ska-sa/mezzanine_cards/SFPP/release/REV0/A/SFP_Led_Mod.pdf

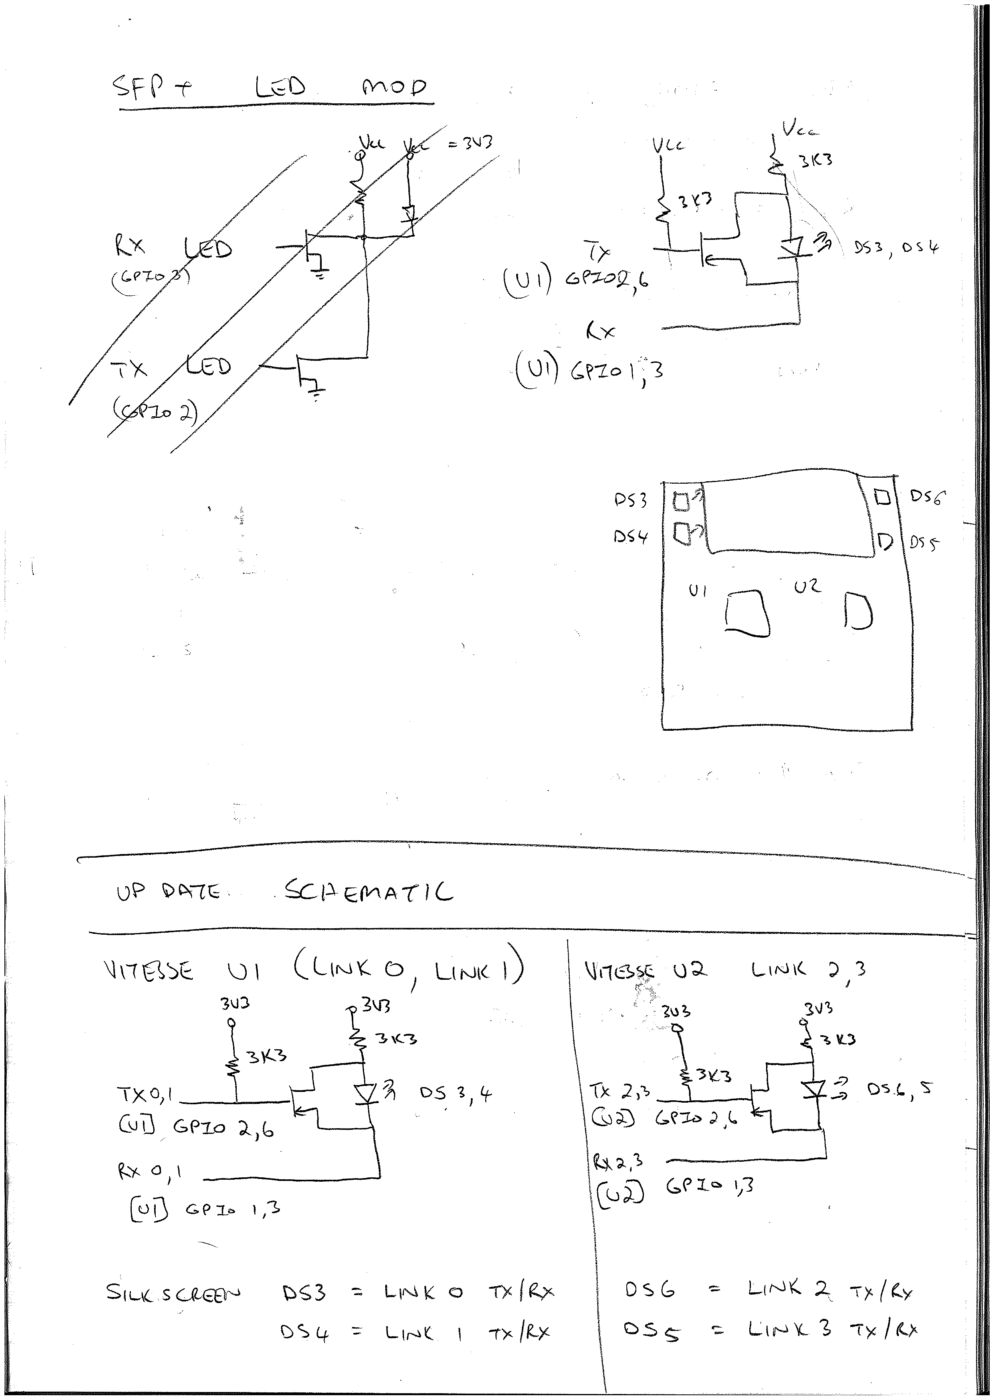
[picture p3: page 1]
